psykokwak-com/TexTime/hardware/electronics/pcb-40x40-integrated/pcb-bottom.png

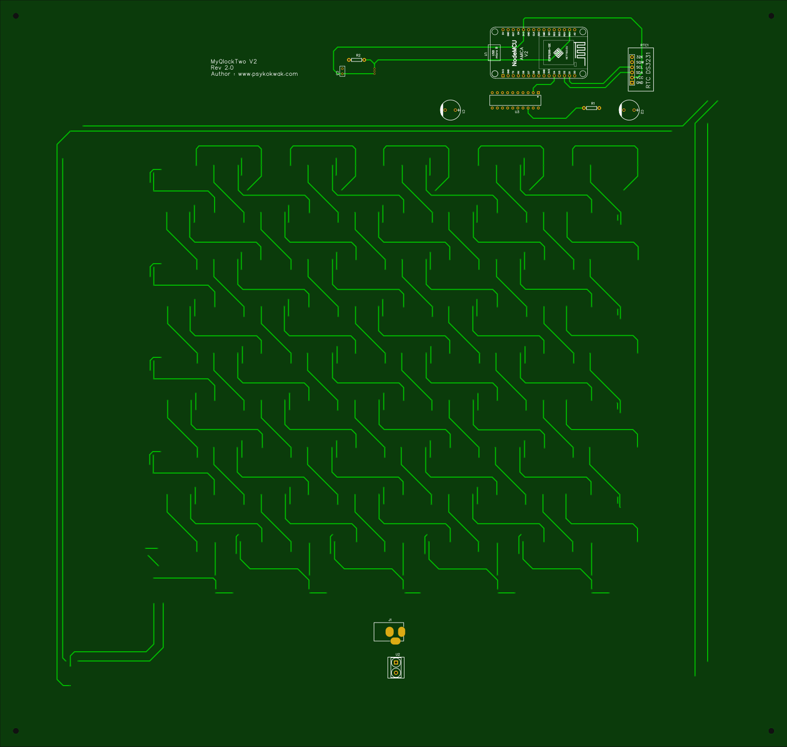
hardware/electronics/pcb-40x40-integrated/pcb-bottom.png
