psykokwak-com/TexTime/hardware/electronics/pcb-40x40-integrated/pcb-layout.png

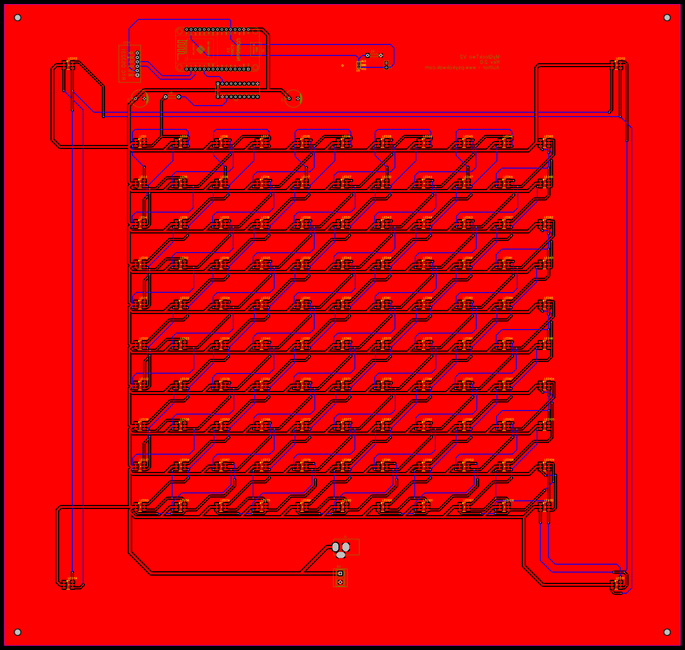
hardware/electronics/pcb-40x40-integrated/pcb-layout.png
