psykokwak-com/TexTime/hardware/electronics/pcb-40x40-integrated/pcb-top.png

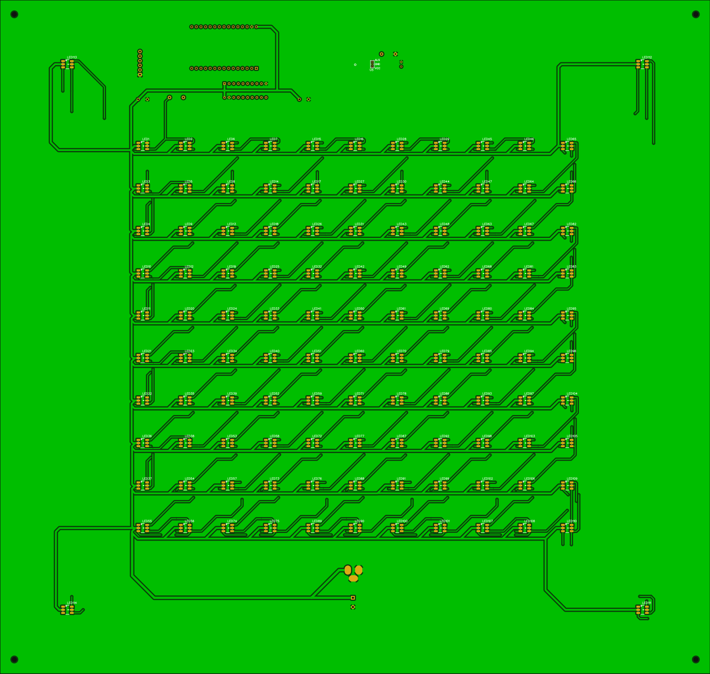
hardware/electronics/pcb-40x40-integrated/pcb-top.png
