psykokwak-com/TexTime/hardware/electronics/pcb-40x40-integrated/photos/2017-12-13-03.jpg

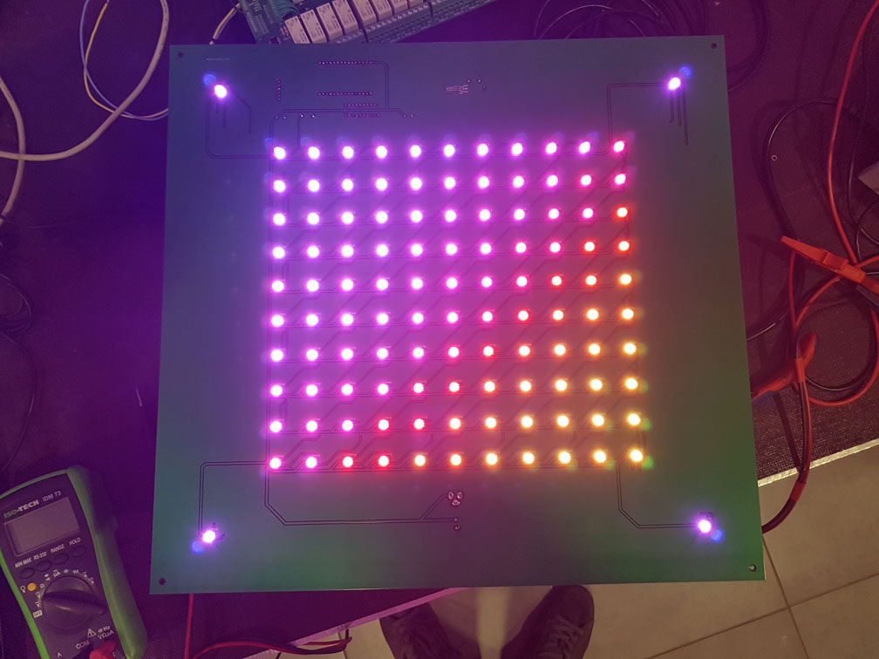
hardware/electronics/pcb-40x40-integrated/photos/2017-12-13-03.jpg
