psykokwak-com/TexTime/hardware/electronics/pcb-40x40-integrated/schematic-leds.png

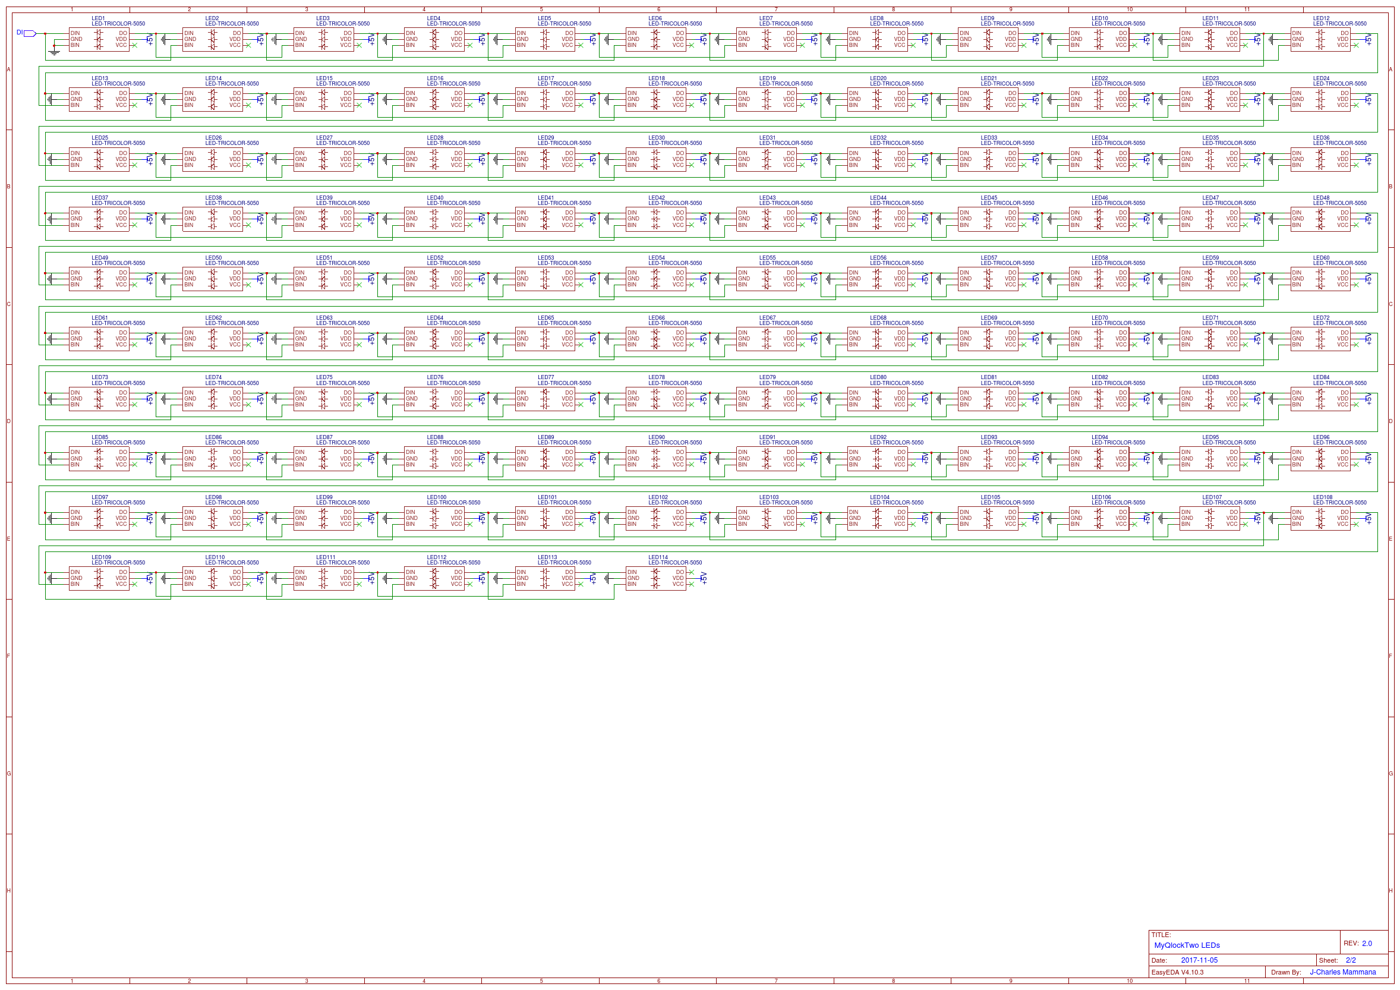
hardware/electronics/pcb-40x40-integrated/schematic-leds.png
