psykokwak-com/TexTime/hardware/electronics/pcb-multi-ledstripe/pcb-bottom.png

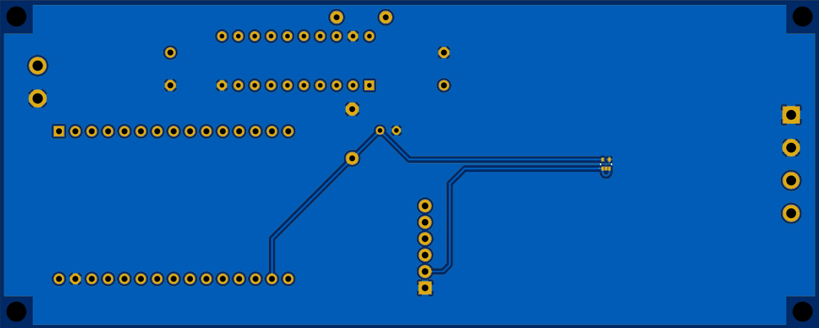
hardware/electronics/pcb-multi-ledstripe/pcb-bottom.png
