psykokwak-com/TexTime/hardware/electronics/pcb-multi-ledstripe/pcb-top.png

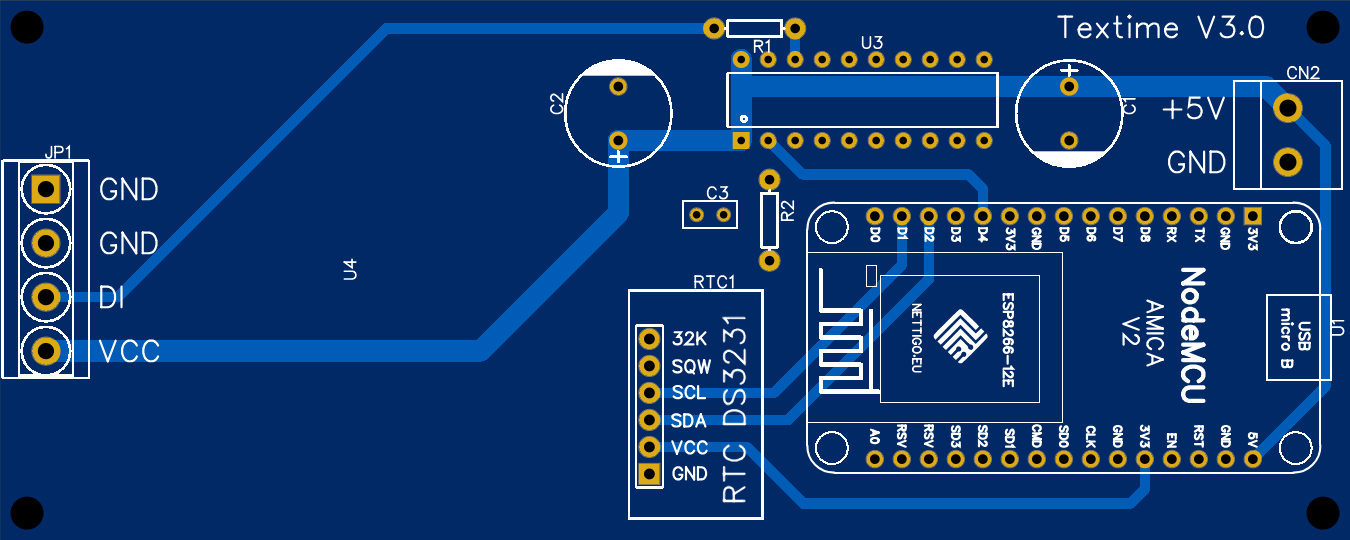
hardware/electronics/pcb-multi-ledstripe/pcb-top.png
