psykokwak-com/TexTime/hardware/electronics/pcb-multi-ledstripe/schematic.png

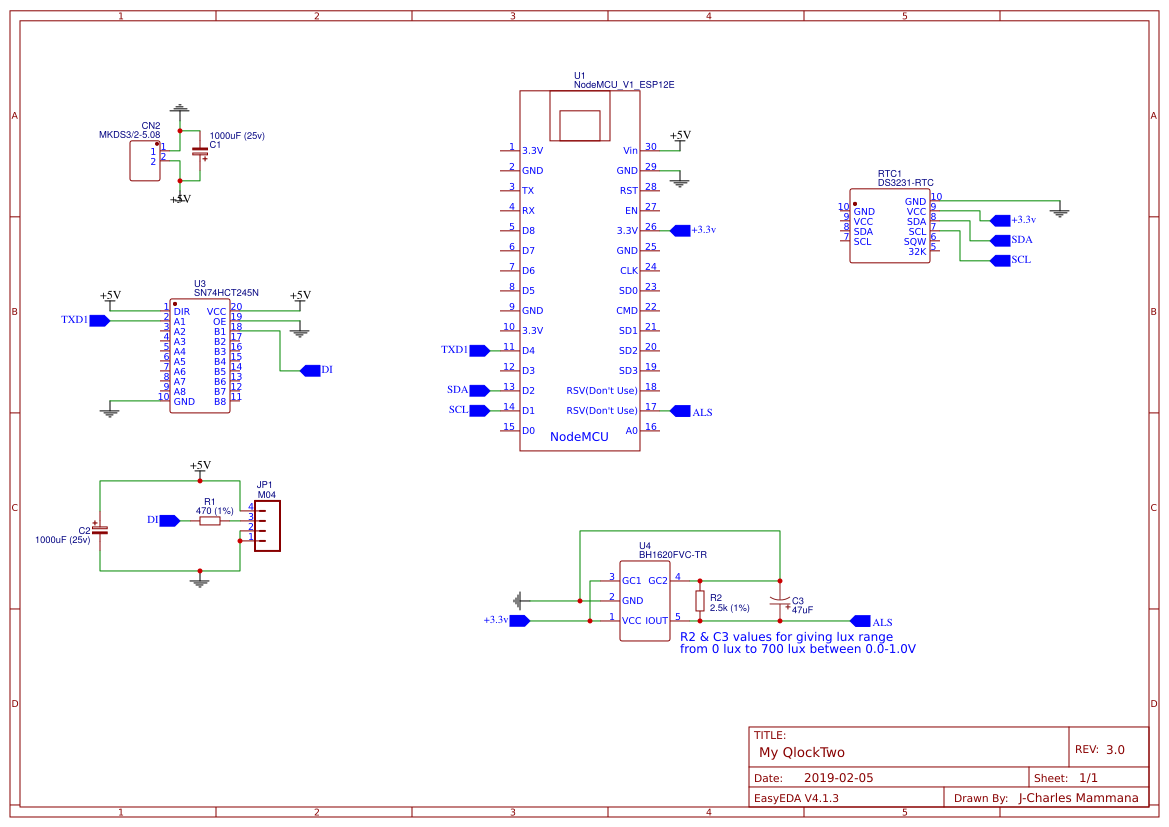
hardware/electronics/pcb-multi-ledstripe/schematic.png
