psykokwak-com/TexTime/firmware/TexTime/global.h

#ifndef GLOBAL_H
#define GLOBAL_H


// A game owns the whole display, and the only deliberate way out is the "Back
// to clock" button. Close the tab, lock the phone or lose the WiFi and the
// clock would stay stuck on a frozen board until someone reopened the page.
// The game pages poll their state endpoint continuously, so that poll doubles
// as a heartbeat: no contact for this long and the clock takes itself back.
#define GAME_IDLE_MS 30000UL
// How often the clock may ask a time server. Zero is the form's documented way
// to say "never", and getNTPtime() honours it; anything else is held between a
// minute and a week, because a small positive value makes the resync test true
// on nearly every pass and hammers a public pool.
#define NTP_INTERVAL_MIN 60L
#define NTP_INTERVAL_MAX 604800L

// Zero passes through untouched: it means "never", not "as often as possible".
inline long clampNtpInterval(long v)
{
  return (v <= 0) ? 0 : constrain(v, NTP_INTERVAL_MIN, NTP_INTERVAL_MAX);
}

#define EEPROM_SIZE 4096
#define SCHEDULER_EEPROM_BASE 1024
#define SCHEDULER_SLOT_SIZE 8

ESP8266HTTPUpdateServer _httpUpdater;
ESP8266WebServer _server(80);
DNSServer _dnsServer;
WiFiClient _mqttWifiClient;
PubSubClient _mqtt(_mqttWifiClient);


struct strConfig {
  boolean dhcp;                         // 1 Byte - EEPROM 16 
  boolean isDayLightSaving;             // 1 Byte - EEPROM 17
  long Update_Time_Via_NTP_Every;       // 4 Byte - EEPROM 18
  long timeZone;                        // 4 Byte - EEPROM 22
  byte  IP[4];                          // 4 Byte - EEPROM 32
  byte  Netmask[4];                     // 4 Byte - EEPROM 36
  byte  Gateway[4];                     // 4 Byte - EEPROM 40
  byte  DNS[4];                         // 4 Byte - EEPROM 44
  String ssid;                          // up to 64 Byte - EEPROM 64
  String password;                      // up to 64 Byte - EEPROM 128
  String ntpServerName;                 // up to 64 Byte - EEPROM 192
  String DeviceName;                    // up to 64 Byte - EEPROM 256

  boolean brightnessAuto;               // 1 Byte - EEPROM 384
  byte brightness;                      // 1 Byte - EEPROM 385
  byte color[4];                        // 4 Byte - EEPROM 386
  byte mode;                            // 1 Byte - EEPROM 390
  byte animation;                       // 1 Byte - EEPROM 391
  byte colorRandom;                     // 1 Byte - EEPROM 392
  byte brightnessAutoMinDay;            // 1 Byte - EEPROM 393
  byte brightnessAutoMinNight;          // 1 Byte - EEPROM 394
  byte ledConfig;                       // 1 Byte - EEPROM 395
  byte luxSensitivity;                  // 1 Byte - EEPROM 396
  byte language;                        // 1 Byte - EEPROM 397
  byte brightnessMax;                   // 1 Byte - EEPROM 398
  byte ledType;                         // 1 Byte - EEPROM 399  (index into LED_TYPES, LedStrip.h)


  String MQTTServer;                    // up to 64 Byte - EEPROM 512
  String MQTTLogin;                     // up to 64 Byte - EEPROM 576
  String MQTTPassword;                  // up to 64 Byte - EEPROM 640
  long MQTTPort;                        // 4 Byte - EEPROM 704
  long MQTTPubInterval;                 // 4 Byte - EEPROM 708


  byte animSpeed;          // 1 Byte - EEPROM 776  (1-20, 10=normal)
  byte animBrightnessMin;  // 1 Byte - EEPROM 777  (0-100 percent)
  byte animBrightnessMax;  // 1 Byte - EEPROM 778  (0-100 percent)

} _config;


// What is on the strip right now, as opposed to what the user has chosen.
//
// Deliberately NOT part of _config. The scheduler overrides these for the
// duration of a time slot and the dashboard sliders override them while you
// drag, and neither is a decision: writing them into _config meant the next
// unrelated WriteConfig() quietly persisted a preview as if it had been picked.
// _config keeps the choice, _live keeps the current appearance.
struct strLiveParams {
  byte animSpeed;             // 1-20, 10 = normal
  byte animBrightnessMin;     // 0-100 percent
  byte animBrightnessMax;     // 0-100 percent

  byte brightnessAutoMinDay;  // 0-255
  byte brightnessAutoMinNight;// 0-255
  byte brightnessMax;         // 0-255, ceiling of the automatic range
  byte luxSensitivity;        // light level that maps to full brightness
} _live;

// Copy the user settings into the live ones. Called at boot and whenever the
// user actually commits a change through the web interface or MQTT.
void syncLiveFromConfig()
{
  _live.animSpeed = _config.animSpeed;
  _live.animBrightnessMin = _config.animBrightnessMin;
  _live.animBrightnessMax = _config.animBrightnessMax;

  _live.brightnessAutoMinDay = _config.brightnessAutoMinDay;
  _live.brightnessAutoMinNight = _config.brightnessAutoMinNight;
  _live.brightnessMax = _config.brightnessMax;
  _live.luxSensitivity = _config.luxSensitivity;
}

// Keep the animation brightness range valid: min must stay strictly below max,
// otherwise the pulsing animations end up with a zero amplitude and freeze.
// The user-supplied max wins and min is pulled underneath it, so moving a
// single slider never silently resets the other one to a default.
//
// Takes a pair rather than reading _config: the same rule has to hold for the
// live values the sliders drive and for the locals a scheduler slot arrives in.
void clampAnimBrightness(byte &lo, byte &hi)
{
  if (lo > 100) lo = 10;
  if (hi > 100) hi = 100;

  if (hi <= lo)
  {
    if (hi < 1) hi = 1;
    lo = hi - 1;
  }
}

void validateAnimBrightness()
{
  clampAnimBrightness(_config.animBrightnessMin, _config.animBrightnessMax);
}

// The LED type is an index into LED_TYPES in LedStrip.h, which is included
// after this file; the count is all the config code needs from it.
int ledTypesCount();

// Entry 0 of LED_TYPES: WS2812 / WS2813, the strip every clock was built with
// before the type became a setting.
#define LED_TYPE_DEFAULT 0

// An EEPROM written before the setting existed holds 0xFF at its address, and
// a crafted request can carry anything: both land on the default rather than
// on an entry past the end of the table.
inline byte sanitizeLedType(int v)
{
  return (v < 0 || v >= ledTypesCount()) ? LED_TYPE_DEFAULT : v;
}


//  Auxiliary function to handle EEPROM

void EEPROMWritelong(int address, long value){
  byte four = (value & 0xFF);
  byte three = ((value >> 8) & 0xFF);
  byte two = ((value >> 16) & 0xFF);
  byte one = ((value >> 24) & 0xFF);

  //Write the 4 bytes into the eeprom memory.
  EEPROM.write(address, four);
  EEPROM.write(address + 1, three);
  EEPROM.write(address + 2, two);
  EEPROM.write(address + 3, one);
}

long EEPROMReadlong(long address){
  //Read the 4 bytes from the eeprom memory.
  long four = EEPROM.read(address);
  long three = EEPROM.read(address + 1);
  long two = EEPROM.read(address + 2);
  long one = EEPROM.read(address + 3);

  //Return the recomposed long by using bit shift.
  return ((four << 0) & 0xFF) + ((three << 8) & 0xFFFF) + ((two << 16) & 0xFFFFFF) + ((one << 24) & 0xFFFFFFFF);
}

// Check the Values is between 0-255
boolean checkRange(String Value){
  int v = Value.toInt();
  return (v >= 0 && v <= 255);
}

// Four decimal parts, each 0-255, and nothing else. The parsers below split on
// dots and call toInt(), which answers 0 for an empty piece -- so without this
// gate a truncated field silently writes a zero octet.
boolean isValidIPv4(const String &s)
{
  int parts = 0, value = 0, digits = 0;

  for (unsigned int i = 0; i <= s.length(); i++)
  {
    // The end of the string closes the last part, exactly like a dot.
    char c = (i < s.length()) ? s[i] : '.';

    if (c >= '0' && c <= '9')
    {
      if (++digits > 3) return false;
      value = value * 10 + (c - '0');
      if (value > 255) return false;
    }
    else if (c == '.')
    {
      if (digits == 0) return false;   // empty part: "", "1..2", ".1.2.3"
      if (++parts > 4) return false;
      value = 0;
      digits = 0;
    }
    else return false;                 // letters, spaces, anything else
  }

  return (parts == 4);
}

void WriteStringToEEPROM(int beginaddress, String string, int maxLen = 63){
  if ((int)string.length() > maxLen) string = string.substring(0, maxLen);
  // The whole 64 byte slot is written, so zero it first: toCharArray only fills
  // up to the terminator and would otherwise leave stack garbage in EEPROM.
  char  charBuf[64] = {0};
  string.toCharArray(charBuf, sizeof(charBuf));
  for (unsigned int t = 0; t < sizeof(charBuf); t++)
  {
    EEPROM.write(beginaddress + t, charBuf[t]);
  }
}

String  ReadStringFromEEPROM(int beginaddress){
  volatile byte counter = 0;
  char rChar;
  String retString = "";

  if (EEPROM.read(beginaddress) == 255)
    return String();

  while (1)
  {
    if (counter >= 64) break;
    rChar = EEPROM.read(beginaddress + counter);
    if (rChar == 0) break;
    counter++;
    retString.concat(rChar);
  }
  return retString;
}


/*
**
** CONFIGURATION HANDLING
**
*/

void ResetEEPROM()
{
  for (int i = 0; i < EEPROM_SIZE; i++)
    EEPROM.write(i, 0xFF);

  EEPROM.commit();
}

void WriteConfig(){

  Serial.println("Writing Config");
  EEPROM.write(0, 'C');
  EEPROM.write(1, 'F');
  EEPROM.write(2, 'G');
  EEPROM.write(3, '2');

  EEPROM.write(16, _config.dhcp);
  EEPROM.write(17, _config.isDayLightSaving);

  EEPROMWritelong(18, _config.Update_Time_Via_NTP_Every); // 4 Byte
  EEPROMWritelong(22, _config.timeZone); // 4 Byte

  EEPROM.write(32, _config.IP[0]);
  EEPROM.write(33, _config.IP[1]);
  EEPROM.write(34, _config.IP[2]);
  EEPROM.write(35, _config.IP[3]);

  EEPROM.write(36, _config.Netmask[0]);
  EEPROM.write(37, _config.Netmask[1]);
  EEPROM.write(38, _config.Netmask[2]);
  EEPROM.write(39, _config.Netmask[3]);

  EEPROM.write(40, _config.Gateway[0]);
  EEPROM.write(41, _config.Gateway[1]);
  EEPROM.write(42, _config.Gateway[2]);
  EEPROM.write(43, _config.Gateway[3]);

  EEPROM.write(44, _config.DNS[0]);
  EEPROM.write(45, _config.DNS[1]);
  EEPROM.write(46, _config.DNS[2]);
  EEPROM.write(47, _config.DNS[3]);

  WriteStringToEEPROM(64, _config.ssid);
  WriteStringToEEPROM(128, _config.password);
  WriteStringToEEPROM(192, _config.ntpServerName);
  WriteStringToEEPROM(256, _config.DeviceName);

  EEPROM.write(384, _config.brightnessAuto);
  EEPROM.write(385, _config.brightness);
  EEPROM.write(386, _config.color[0]); // R
  EEPROM.write(387, _config.color[1]); // G
  EEPROM.write(388, _config.color[2]); // B
  EEPROM.write(389, _config.color[3]); // W
  EEPROM.write(390, _config.mode);
  EEPROM.write(391, _config.animation);
  EEPROM.write(392, _config.colorRandom);
  EEPROM.write(393, _config.brightnessAutoMinDay);
  EEPROM.write(394, _config.brightnessAutoMinNight);
  EEPROM.write(395, _config.ledConfig);
  EEPROM.write(396, _config.luxSensitivity);
  EEPROM.write(397, _config.language);
  EEPROM.write(398, _config.brightnessMax);
  EEPROM.write(399, _config.ledType);

  WriteStringToEEPROM(512, _config.MQTTServer);
  WriteStringToEEPROM(576, _config.MQTTLogin);
  WriteStringToEEPROM(640, _config.MQTTPassword);
  EEPROMWritelong(704, _config.MQTTPort);
  EEPROMWritelong(708, _config.MQTTPubInterval);


  EEPROM.write(776, _config.animSpeed);
  EEPROM.write(777, _config.animBrightnessMin);
  EEPROM.write(778, _config.animBrightnessMax);

  EEPROM.commit();
}

boolean ReadConfig(){
  Serial.println("Reading Configuration");
  if (EEPROM.read(0) == 'C' && EEPROM.read(1) == 'F'  && EEPROM.read(2) == 'G' && EEPROM.read(3) == '2')
  {
    Serial.println("Configuration Found!");
    _config.dhcp = 	EEPROM.read(16);
    _config.isDayLightSaving = EEPROM.read(17);
    _config.Update_Time_Via_NTP_Every = EEPROMReadlong(18); // 4 Byte
    _config.Update_Time_Via_NTP_Every = clampNtpInterval(_config.Update_Time_Via_NTP_Every);
    _config.timeZone = EEPROMReadlong(22); // 4 Byte
    if (_config.timeZone < -120 || _config.timeZone > 130) _config.timeZone = 10; // sanity check (unit = 1/10th hour)
    _config.IP[0] = EEPROM.read(32);
    _config.IP[1] = EEPROM.read(33);
    _config.IP[2] = EEPROM.read(34);
    _config.IP[3] = EEPROM.read(35);
    _config.Netmask[0] = EEPROM.read(36);
    _config.Netmask[1] = EEPROM.read(37);
    _config.Netmask[2] = EEPROM.read(38);
    _config.Netmask[3] = EEPROM.read(39);
    _config.Gateway[0] = EEPROM.read(40);
    _config.Gateway[1] = EEPROM.read(41);
    _config.Gateway[2] = EEPROM.read(42);
    _config.Gateway[3] = EEPROM.read(43);
    _config.DNS[0] = EEPROM.read(44);
    _config.DNS[1] = EEPROM.read(45);
    _config.DNS[2] = EEPROM.read(46);
    _config.DNS[3] = EEPROM.read(47);
    _config.ssid = ReadStringFromEEPROM(64);
    _config.password = ReadStringFromEEPROM(128);
    _config.ntpServerName = ReadStringFromEEPROM(192);
    _config.DeviceName = ReadStringFromEEPROM(256);

    // Application parameters here ... from EEPROM 192 to 511
    _config.brightnessAuto = EEPROM.read(384);
    _config.brightness = EEPROM.read(385);
    _config.color[0] = EEPROM.read(386); // R
    _config.color[1] = EEPROM.read(387); // G
    _config.color[2] = EEPROM.read(388); // B
    _config.color[3] = EEPROM.read(389); // W
    _config.mode = EEPROM.read(390);
    _config.animation = EEPROM.read(391);
    if (_config.animation > 14) _config.animation = 0;
    _config.colorRandom = EEPROM.read(392);
    _config.brightnessAutoMinDay = EEPROM.read(393);
    _config.brightnessAutoMinNight = EEPROM.read(394);
    _config.brightnessMax = EEPROM.read(398);
    if (_config.brightnessMax < 1) _config.brightnessMax = 255;
    _config.ledConfig = EEPROM.read(395);
    _config.luxSensitivity = EEPROM.read(396);
    // Zero would collapse the automatic brightness range onto a single point and
    // divide by zero in the map() below. Not reachable from the dashboard, whose
    // list starts at 10, but reachable by a crafted request or the legacy route.
    if (_config.luxSensitivity < 1) _config.luxSensitivity = 40;
    _config.language = EEPROM.read(397);
    // Byte 399 was never written before the LED type existed, so a clock
    // upgraded in place reads 0xFF here and keeps its WS2812 / WS2813 strip.
    _config.ledType = sanitizeLedType(EEPROM.read(399));

    _config.MQTTServer = ReadStringFromEEPROM(512);
    _config.MQTTLogin = ReadStringFromEEPROM(576);
    _config.MQTTPassword = ReadStringFromEEPROM(640);
    _config.MQTTPort = EEPROMReadlong(704);
    _config.MQTTPubInterval = EEPROMReadlong(708);


    _config.animSpeed = EEPROM.read(776);
    if (_config.animSpeed < 1 || _config.animSpeed > 20) _config.animSpeed = 10;
    _config.animBrightnessMin = EEPROM.read(777);
    _config.animBrightnessMax = EEPROM.read(778);
    validateAnimBrightness();

    syncLiveFromConfig();

    return true;

  }
  else
  {
    Serial.println("Configuration NOT FOUND!!!!");
    ResetEEPROM();
    return false;
  }
}


void printConfig(){

  Serial.println("Printing Config");

  Serial.printf("DHCP:%d\n", _config.dhcp);
  Serial.printf("DayLight:%d\n", _config.isDayLightSaving);

  Serial.printf("NTP update every %ld sec\n", _config.Update_Time_Via_NTP_Every); // 4 Byte
  Serial.printf("Timezone %ld\n", _config.timeZone); // 4 Byte

  Serial.printf("IP:%d.%d.%d.%d\n", _config.IP[0],_config.IP[1],_config.IP[2],_config.IP[3]);
  Serial.printf("Mask:%d.%d.%d.%d\n", _config.Netmask[0],_config.Netmask[1],_config.Netmask[2],_config.Netmask[3]);
  Serial.printf("Gateway:%d.%d.%d.%d\n", _config.Gateway[0], _config.Gateway[1], _config.Gateway[2], _config.Gateway[3]);
  Serial.printf("DNS:%d.%d.%d.%d\n", _config.DNS[0], _config.DNS[1], _config.DNS[2], _config.DNS[3]);

 
  Serial.printf("SSID:%s\n", _config.ssid.c_str());
  Serial.printf("PWD:***\n");
  Serial.printf("NTP ServerName:%s\n", _config.ntpServerName.c_str());
  Serial.printf("Device Name:%s\n", _config.DeviceName.c_str());

  // Application Settings here... from EEPROM 192 up to 511 (0 - 511)
  Serial.printf("Brightness auto:%d\n", _config.brightnessAuto);
  Serial.printf("Brightness:%d\n", _config.brightness);
  Serial.printf("Color:%02X%02X%02X%02X\n", _config.color[0], _config.color[1], _config.color[2], _config.color[3]);
  Serial.printf("Mode:%d\n", _config.mode);
  Serial.printf("Animation:%d\n", _config.animation);
  Serial.printf("Color Random:%d\n", _config.colorRandom);
  Serial.printf("Minimum brightness auto during the day:%d\n", _config.brightnessAutoMinDay);
  Serial.printf("Minimum brightness auto during the night:%d\n", _config.brightnessAutoMinNight);
  Serial.printf("Max brightness:%d\n", _config.brightnessMax);
  Serial.printf("Led Configuration:%d\n", _config.ledConfig);
  Serial.printf("Led Type:%d\n", _config.ledType);
}


int32_t GetRSSIinPercent(int32_t rssi)
{
  int quality = 0;
  if (rssi <= -100)
  {
    quality = 0;
  }
  else if (rssi >= -50)
  {
    quality = 100;
  }
  else
  {
    quality = 2 * (rssi + 100);
  }
  return quality;
}

String GetMacAddress(){
  uint8_t mac[6];
  char macStr[18] = {0};
  WiFi.macAddress(mac);
  sprintf(macStr, "%02X:%02X:%02X:%02X:%02X:%02X", mac[0],  mac[1], mac[2], mac[3], mac[4], mac[5]);
  return  String(macStr);
}

String GetAPMacAddress(){
  uint8_t mac[6];
  char macStr[18] = {0};
  WiFi.softAPmacAddress(mac);
  sprintf(macStr, "%02X:%02X:%02X:%02X:%02X:%02X", mac[0],  mac[1], mac[2], mac[3], mac[4], mac[5]);
  return  String(macStr);
}

uint64_t millis64() {
  static uint32_t low32, high32;
  uint32_t new_low32 = millis();
  if (new_low32 < low32) high32++;
  low32 = new_low32;
  return (uint64_t)high32 << 32 | low32;
}

void toggleLed(unsigned long counter)
{
  static int p = 0;

  int v = (counter % 2);

  if (v != p)
    digitalWrite(LED_BUILTIN, v);

  p = v;
}

String dec2hex2(byte v)
{
  String s = String((int)(v), HEX);

  if (v < 0x10)
    s = "0" + s;

  s.toUpperCase();

  return s;
}


class Frame
{
private:
  double _fps;
  uint64_t _framePrevious;

public:
  Frame() :
    _fps(10),
    _framePrevious(0)
  {
  }

  void init(double fps)
  {
    // A null or negative rate would make next() divide by zero and freeze the
    // animation for good, so never let the frame rate fall out of range.
    if (fps < 0.1) fps = 0.1;

    _fps = fps;
    _framePrevious = 0;
  }

  bool next()
  {
    uint64_t frame = millis64();

    if (frame - _framePrevious < (1000.0 / _fps))
      return false;

    _framePrevious = frame;
    return true;
  }
};

#endif
