psykokwak-com/TexTime/firmware/TexTime/Page_ico.h

//
//  HTML PAGE
//

// http://tools.garry.tv/bin2c/

int PAGE_ico_size = 21042;
const char PAGE_ico[] PROGMEM =
{
  137, 80, 78, 71, 13, 10, 26, 10, 0, 0, 0, 13, 73, 72, 68, 82, 0, 0, 0, 128, 0, 0, 0, 128, 8, 6, 0, 0, 0, 195, 62,
  97, 203, 0, 0, 0, 25, 116, 69, 88, 116, 83, 111, 102, 116, 119, 97, 114, 101, 0, 65, 100, 111, 98, 101, 32,
  73, 109, 97, 103, 101, 82, 101, 97, 100, 121, 113, 201, 101, 60, 0, 0, 3, 102, 105, 84, 88, 116, 88, 77,
  76, 58, 99, 111, 109, 46, 97, 100, 111, 98, 101, 46, 120, 109, 112, 0, 0, 0, 0, 0, 60, 63, 120, 112, 97, 99,
  107, 101, 116, 32, 98, 101, 103, 105, 110, 61, 34, 239, 187, 191, 34, 32, 105, 100, 61, 34, 87, 53, 77,
  48, 77, 112, 67, 101, 104, 105, 72, 122, 114, 101, 83, 122, 78, 84, 99, 122, 107, 99, 57, 100, 34, 63, 62,
  32, 60, 120, 58, 120, 109, 112, 109, 101, 116, 97, 32, 120, 109, 108, 110, 115, 58, 120, 61, 34, 97, 100,
  111, 98, 101, 58, 110, 115, 58, 109, 101, 116, 97, 47, 34, 32, 120, 58, 120, 109, 112, 116, 107, 61, 34,
  65, 100, 111, 98, 101, 32, 88, 77, 80, 32, 67, 111, 114, 101, 32, 53, 46, 48, 45, 99, 48, 54, 49, 32, 54,
  52, 46, 49, 52, 48, 57, 52, 57, 44, 32, 50, 48, 49, 48, 47, 49, 50, 47, 48, 55, 45, 49, 48, 58, 53, 55, 58,
  48, 49, 32, 32, 32, 32, 32, 32, 32, 32, 34, 62, 32, 60, 114, 100, 102, 58, 82, 68, 70, 32, 120, 109, 108,
  110, 115, 58, 114, 100, 102, 61, 34, 104, 116, 116, 112, 58, 47, 47, 119, 119, 119, 46, 119, 51, 46, 111,
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
  97, 62, 32, 60, 63, 120, 112, 97, 99, 107, 101, 116, 32, 101, 110, 100, 61, 34, 114, 34, 63, 62, 13, 172,
  68, 163, 0, 0, 78, 98, 73, 68, 65, 84, 120, 218, 236, 189, 121, 176, 109, 215, 89, 31, 248, 173, 61, 158,
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
};
