psykokwak-com/TexTime/firmware/TexTime/Page_general.h

void send_general_configuration_values_html()
{
	String values = "";
  values += "brightnessauto|" + (String)(_config.brightnessAuto ? "checked" : "") + "|chk\n";
  values += "brightness|" + (String)_config.brightness + "|input\n";
  values += "brightnessday|" + (String)_config.brightnessAutoMinDay + "|input\n";
  values += "brightnessnight|" + (String)_config.brightnessAutoMinNight + "|input\n";
  values += "brightnessmax|" + (String)_config.brightnessMax + "|input\n";
  values += "color|#" + dec2hex2(_config.color[0]) + dec2hex2(_config.color[1]) + dec2hex2(_config.color[2]) + "|input\n";
  values += "colorText|#" + dec2hex2(_config.color[0]) + dec2hex2(_config.color[1]) + dec2hex2(_config.color[2]) + "|input\n";
  values += "lang|" + (String)_config.language + "|input\n";
  values += "mode|" + (String)_config.mode + "|input\n";
  values += "animation|" + (String)_config.animation + "|input\n";
  values += "colorrandom|" + (String)_config.colorRandom + "|input\n";
  values += "ledconfig|" + (String)_config.ledConfig + "|input\n";
  values += "ledtype|" + (String)_config.ledType + "|input\n";
  values += "brightnesssensibility|" + (String)_config.luxSensitivity + "|input\n";
  values += "animspeed|" + (String)_config.animSpeed + "|input\n";
  values += "animbrightmin|" + (String)_config.animBrightnessMin + "|input\n";
  values += "animbrightmax|" + (String)_config.animBrightnessMax + "|input\n";

	_server.send(200, "text/plain", values);
	//Serial.println(__FUNCTION__); 
}

void send_general_ledconfig_values_html()
{
  cl_Lst<LedConfiguration *> *pl = QTLed.getLedConfigurationList();

  String values = "";
  for (int i = 0; i < pl->size(); i++)
    values += "ledconfig|" + (*pl)[i]->getName() + "|select\n";

  _server.send(200, "text/plain", values);
}

void send_general_ledtype_values_html()
{
  String values = "";
  for (int i = 0; i < QTLed.getLedTypesCount(); i++)
    values += "ledtype|" + QTLed.getLedTypeName(i) + "|select\n";

  _server.send(200, "text/plain", values);
}

void send_general_langs_values_html()
{
  cl_Lst<TextTime *> *pl = QTLed.getLanguagesList();

  String values = "";
  for (int i = 0; i < pl->size(); i++)
    values += "lang|" + (*pl)[i]->getLanguage() + "|select\n";

  _server.send(200, "text/plain", values);
}

void send_general_modes_values_html()
{
  cl_Lst<LedStripMode *> *pl = QTLed.getModesList();

  String values = "";
  for (int i = 0; i < pl->size(); i++)
    values += "mode|" + (*pl)[i]->getName() + "|select\n";

  _server.send(200, "text/plain", values);
}

void send_general_animations_values_html()
{
  cl_Lst<LedStripAnimation *> *pl = QTLed.getAnimationsList();

  String values = "";
  for (int i = 0; i < pl->size(); i++)
    values += "animation|" + (*pl)[i]->getName() + "|select\n";

  _server.send(200, "text/plain", values);
}

void send_lang_value_html()
{
  _server.send(200, "text/plain", String(_config.language));
}

// Live preview. Everything here writes _live, never _config: dragging a slider
// is not a decision, and writing _config meant the next unrelated save quietly
// persisted whatever the slider happened to be on. /admin/save/general is what
// commits a choice.
void send_general_led()
{
  if (_server.args() > 0)
  {
    for (uint8_t i = 0; i < _server.args(); i++) {
      if (_server.argName(i) == "brightness")
      {
        int b = _server.arg(i).toInt();
        if (b < 0)
          QTLed.setAutomaticBrightness(true);
        else
        {
          QTLed.setAutomaticBrightness(false);
          QTLed.setBrightness(_server.arg(i).toInt());
        }
      }

      if (_server.argName(i) == "brightnessday")
        _live.brightnessAutoMinDay = _server.arg(i).toInt();

      if (_server.argName(i) == "brightnessnight")
        _live.brightnessAutoMinNight = _server.arg(i).toInt();

      if (_server.argName(i) == "brightnessmax")
        _live.brightnessMax = constrain(_server.arg(i).toInt(), 1, 255);

      if (_server.argName(i) == "lang")
      {
        QTLed.setLanguage(_server.arg(i).toInt());
      }

      if (_server.argName(i) == "mode")
      {
        QTLed.setMode(_server.arg(i).toInt());
      }

      if (_server.argName(i) == "color")
      {
        String colorStr = _server.arg(i);
        // Remove # if present
        if (colorStr.startsWith("#")) {
          colorStr = colorStr.substring(1);
        }
        int32_t l = strtol(colorStr.c_str(), 0, 16);
        byte r = (l >> 16) & 0xFF;
        byte g = (l >> 8) & 0xFF;
        byte b = (l >> 0) & 0xFF;

        QTLed.setColor(r, g, b);
      }

      if (_server.argName(i) == "animation")
      {
        QTLed.setAnimation(_server.arg(i).toInt());
      }

      if (_server.argName(i) == "colorrandom")
      {
        QTLed.setColorRandom((RandomColorMode)_server.arg(i).toInt());
      }
      if (_server.argName(i) == "brightnesssensibility")
        _live.luxSensitivity = constrain(_server.arg(i).toInt(), 1, 255);

      if (_server.argName(i) == "animspeed")
        QTLed.setAnimSpeed(constrain(_server.arg(i).toInt(), 1, 20));

      if (_server.argName(i) == "animbrightmin")
        _live.animBrightnessMin = constrain(_server.arg(i).toInt(), 0, 100);

      if (_server.argName(i) == "animbrightmax")
        _live.animBrightnessMax = constrain(_server.arg(i).toInt(), 0, 100);
    }

    clampAnimBrightness(_live.animBrightnessMin, _live.animBrightnessMax);
  }
  _server.send(200, "text/plain", "OK");
}
