psykokwak-com/TexTime/firmware/TexTime/Page_mqtt.h

//
//   FILL THE PAGE WITH VALUES
//

void send_mqtt_configuration_values_html()
{
  String values = "";

  values += "host|" + (String)_config.MQTTServer + "|input\n";
  values += "port|" + String(_config.MQTTPort) + "|input\n";
  values += "login|" + (String)_config.MQTTLogin + "|input\n";
  values += "mqttpassword|" + (String)_config.MQTTPassword + "|input\n";
  values += "interval|" + String(_config.MQTTPubInterval) + "|input\n";

  String sublist;
  sublist += "\"" + mqttTopicSubLedColor.topic() + "\" : set display color. Value in hex. eg : #00FF00<br>";
  sublist += "\"" + mqttTopicSubLedMode.topic() + "\" : set display mode. Value in dec. eg : 1<br>";
  sublist += "\"" + mqttTopicSubLedAnim.topic() + "\" : set display animation. Value in dec. eg : 3<br>";
  sublist += "<i>Empty payload returns current value. See publishing \"stat\" topics.</i><br>";

  String publist;
  publist += "\"" + mqttTopicPubLedColor.topic() + "\" : get display color. Value in hex. eg : #00FF00<br>";
  publist += "\"" + mqttTopicPubLedMode.topic() + "\" : get display mode. Value in dec. eg : 1<br>";
  publist += "\"" + mqttTopicPubLedAnim.topic() + "\" : get display animation. Value in dec. eg : 3<br>";
  publist += "<br>";
  publist += "\"" + mqttTopicPubTemp.topic() + "\" : get temperature. Value in degrees celius.<br>";
  publist += "\"" + mqttTopicPubLight.topic() + "\" : get ambient light. Value in lumens.<br>";
  publist += "\"" + mqttTopicPubRssi.topic() + "\" : get WiFi RSSI. Value in %.<br>";

  values += "sublist|" + sublist + "|div\n";
  values += "publist|" + publist + "|div\n";

  _server.sendHeader("Cache-Control", "no-cache, no-store, must-revalidate");
  _server.sendHeader("Pragma", "no-cache");
  _server.sendHeader("Expires", "-1");

  _server.send(200, "text/plain", values);
  //Serial.println(__FUNCTION__);
}

void send_mqtt_connection_values_html()
{
  String s = "";
  switch (_mqtt.state())
  {
  case MQTT_CONNECTION_TIMEOUT: s = "MQTT_CONNECTION_TIMEOUT"; break;
  case MQTT_CONNECTION_LOST: s = "MQTT_CONNECTION_LOST"; break;
  case MQTT_CONNECT_FAILED: s = "MQTT_CONNECT_FAILED"; break;
  case MQTT_DISCONNECTED: s = "MQTT_DISCONNECTED"; break;
  case MQTT_CONNECTED: s = "MQTT_CONNECTED"; break;
  case MQTT_CONNECT_BAD_PROTOCOL: s = "MQTT_CONNECT_BAD_PROTOCOL"; break;
  case MQTT_CONNECT_BAD_CLIENT_ID: s = "MQTT_CONNECT_BAD_CLIENT_ID"; break;
  case MQTT_CONNECT_UNAVAILABLE: s = "MQTT_CONNECT_UNAVAILABLE"; break;
  case MQTT_CONNECT_BAD_CREDENTIALS: s = "MQTT_CONNECT_BAD_CREDENTIALS"; break;
  case MQTT_CONNECT_UNAUTHORIZED: s = "MQTT_CONNECT_UNAUTHORIZED"; break;
  default: s = "MQTT_UNKNOW_ERROR"; break;
  }

  String values = "";
  values += "mqttconnectionstate|" + s + "|div\n";

  _server.sendHeader("Cache-Control", "no-cache, no-store, must-revalidate");
  _server.sendHeader("Pragma", "no-cache");
  _server.sendHeader("Expires", "-1");

  _server.send(200, "text/plain", values);
  //Serial.println(__FUNCTION__);
}
